Mantaj-C/autonomous-forklift/src/Client.h

///////////////////////////////////////////////////////////////////
// Prepared for BCIT ELEX4618, April 2022, by Craig Hennessey
///////////////////////////////////////////////////////////////////
#pragma once

#include <string>
#include <opencv2/opencv.hpp>

//#define WIN4618
#define PI4618

#ifdef WIN4618
#include "Winsock2.h"
#endif

#ifdef PI4618
#define INVALID_SOCKET -1
#define SOCKET_ERROR -1
typedef int SOCKET;
#include <sys/types.h>
#include <stdlib.h>
#include <unistd.h>
#include <sys/socket.h>
#include <sys/ioctl.h>
#include <fcntl.h>
#include <netinet/in.h>
#include <arpa/inet.h>
#include <netdb.h>
#include <thread>
#endif

class CClient
{
private:
#ifdef WIN4618
  WSADATA _wsdat;
#endif

  int _port;
  std::string _addr;
  SOCKET _socket;
  
  bool setblocking(SOCKET fd, bool blocking);

public:
  CClient();
	~CClient();

  void connect_socket(std::string addr, int port);
  void close_socket();

  void tx_str(std::string str);
  bool rx_str(std::string &str);
  bool rx_im(cv::Mat &im);
};
